BlasRam/Proyecto_3_2026/Sistema_IAQ_LoRa/Sistema_IAQ_LoRa/images/1.jpeg

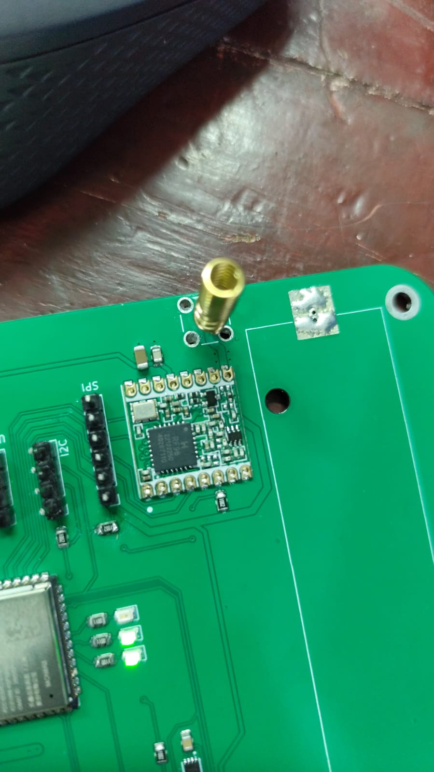
Sistema_IAQ_LoRa/Sistema_IAQ_LoRa/images/1.jpeg
