BlasRam/Proyecto_3_2026/Sistema_IAQ_LoRa/Sistema_IAQ_LoRa/images/5.jpeg

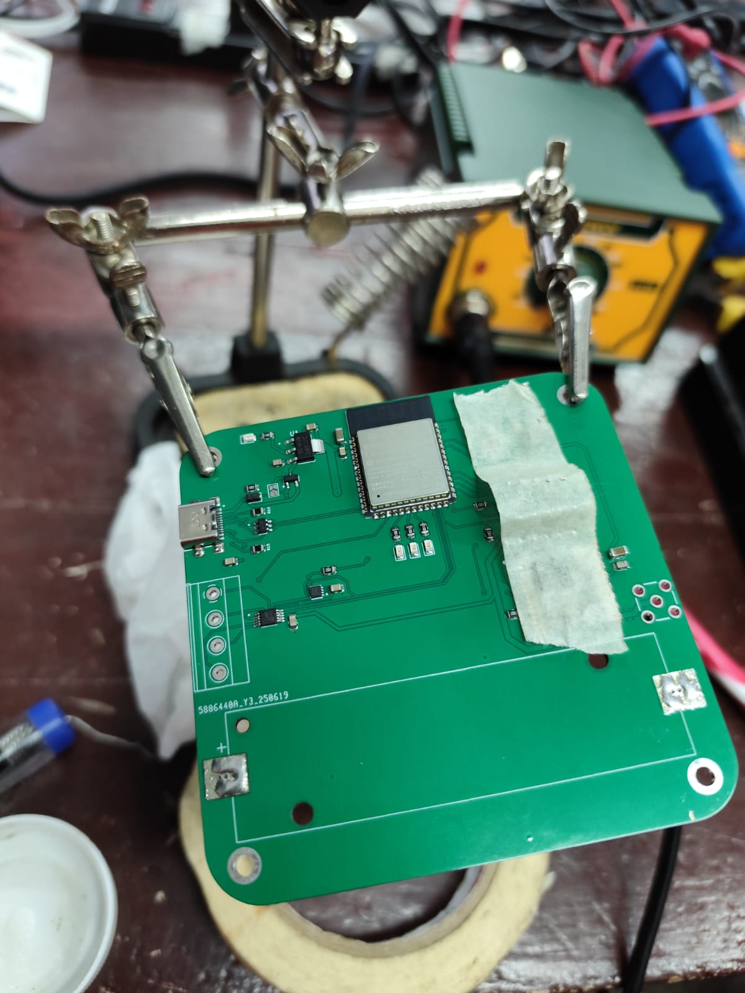
Sistema_IAQ_LoRa/Sistema_IAQ_LoRa/images/5.jpeg
