BlasRam/Proyecto_3_2026/Sistema_IAQ_LoRa/Sistema_IAQ_LoRa/images/6.png

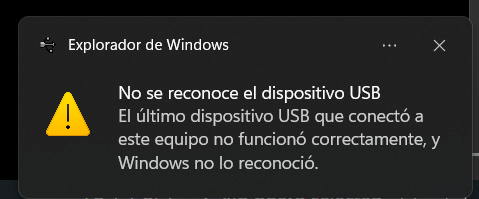
Sistema_IAQ_LoRa/Sistema_IAQ_LoRa/images/6.png
